segfau-yama/dxxk_mouse/dick_mouse/tests/device/speaker.rs

#![no_std]
#![no_main]
#![allow(unexpected_cfgs)]

esp_bootloader_esp_idf::esp_app_desc!();

#[cfg(test)]
#[embedded_test::tests]
mod tests {
    use core::assert_eq;

    use dick_mouse::device::Speaker;

    #[test]
    fn speakerはbufferを更新する() {
        let speaker = Speaker::new([0, -1]).update([-2, -3]);

        assert_eq!(speaker.buffer(), &[-2, -3]);
    }
}
